humor4fun/NFC-Cartridge-Player/3d print files/mods/vhs_player_slot_w_support.stl

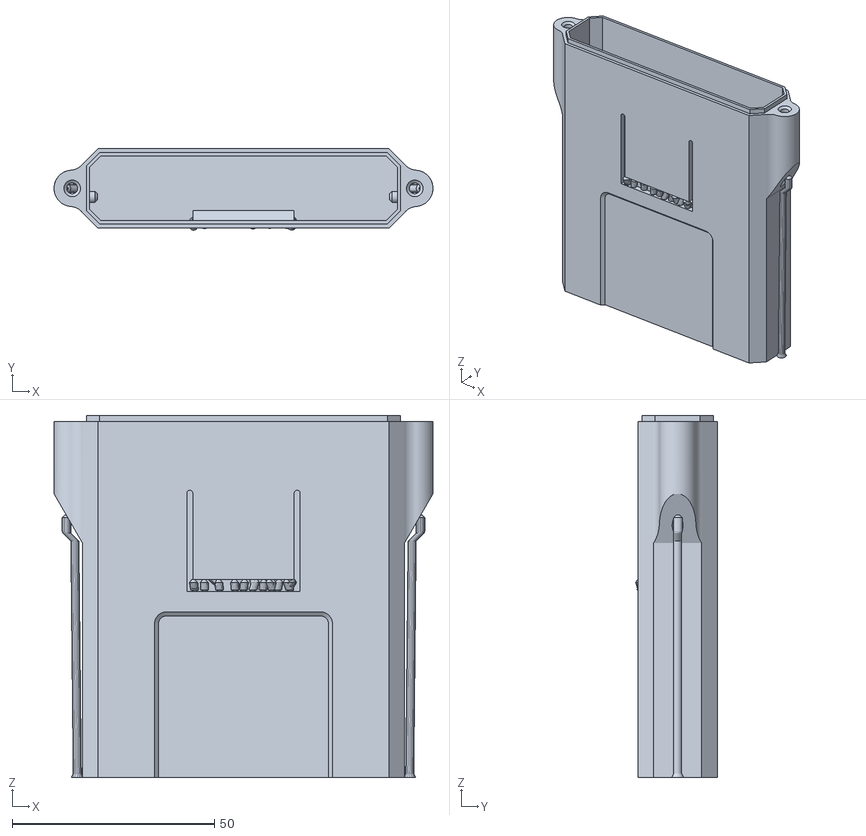
[picture p21: CAD file, 2026-01-05]
3d print files/mods/vhs_player_slot_w_support.stl
93.6 x 20.2 x 89.5
