humor4fun/NFC-Cartridge-Player/3d print files/Player/cartridge-player_bottom.3mf

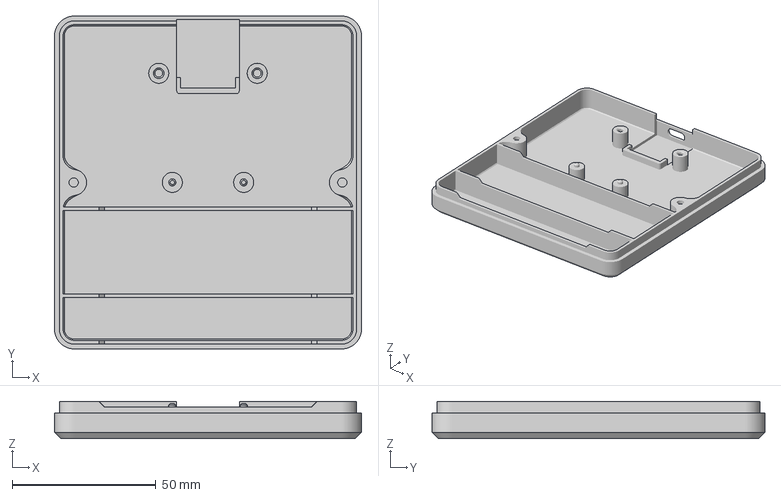
[picture p22: CAD file, 2026-01-05]
3d print files/Player/cartridge-player_bottom.3mf
107.0 x 116.0 x 13.0 mm
