humor4fun/NFC-Cartridge-Player/3d print files/Flip cartridge box/Cartridge/Cartridge+Top.stl

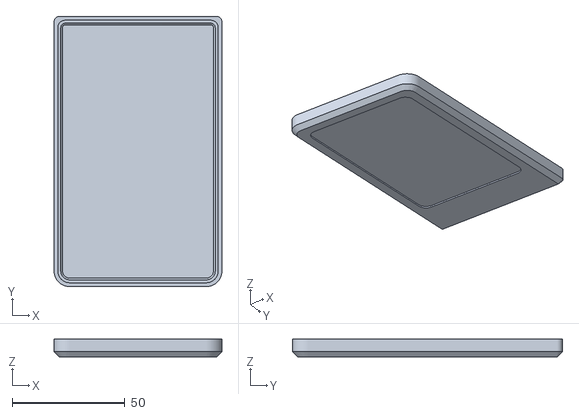
[picture p24: CAD file, 2026-01-05]
3d print files/Flip cartridge box/Cartridge/Cartridge+Top.stl
74.6 x 120.0 x 7.80
