humor4fun/NFC-Cartridge-Player/3d print files/mods/multi-part-cartridge/cartridge-label.stl

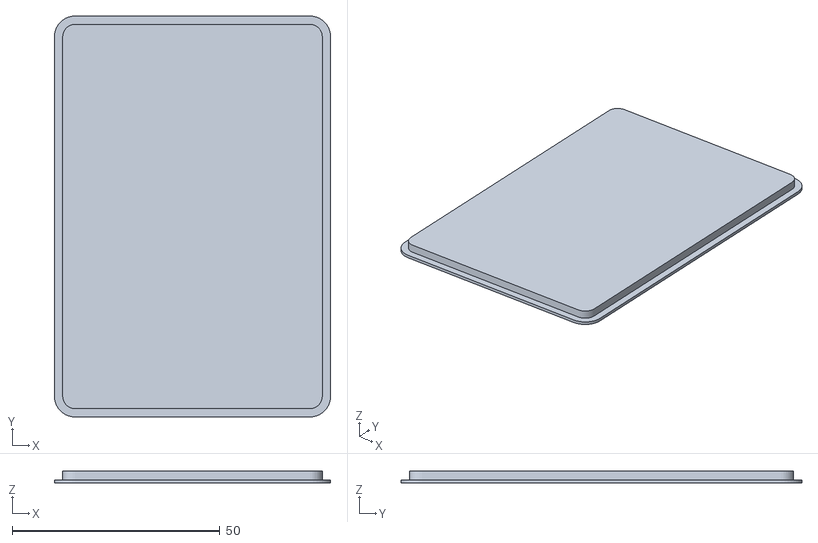
[picture p25: CAD file, 2026-01-05]
3d print files/mods/multi-part-cartridge/cartridge-label.stl
66.5 x 96.5 x 3.00
