humor4fun/NFC-Cartridge-Player/3d print files/Player/cartridge-player_bottom_buzzer.3mf

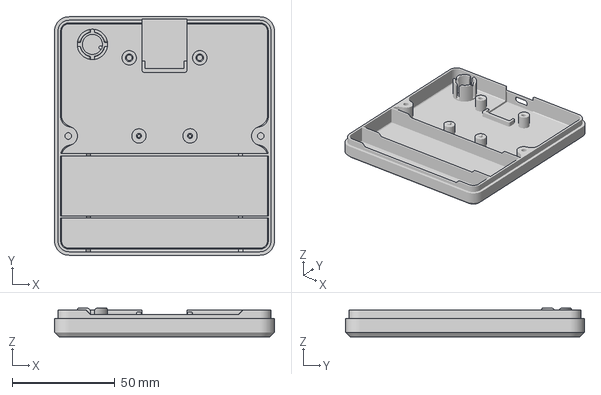
[picture p26: CAD file, 2026-01-05]
3d print files/Player/cartridge-player_bottom_buzzer.3mf
107.0 x 116.0 x 14.0 mm
