humor4fun/NFC-Cartridge-Player/3d print files/Flip cartridge box/Box/cartridge-box-8-slot.stl

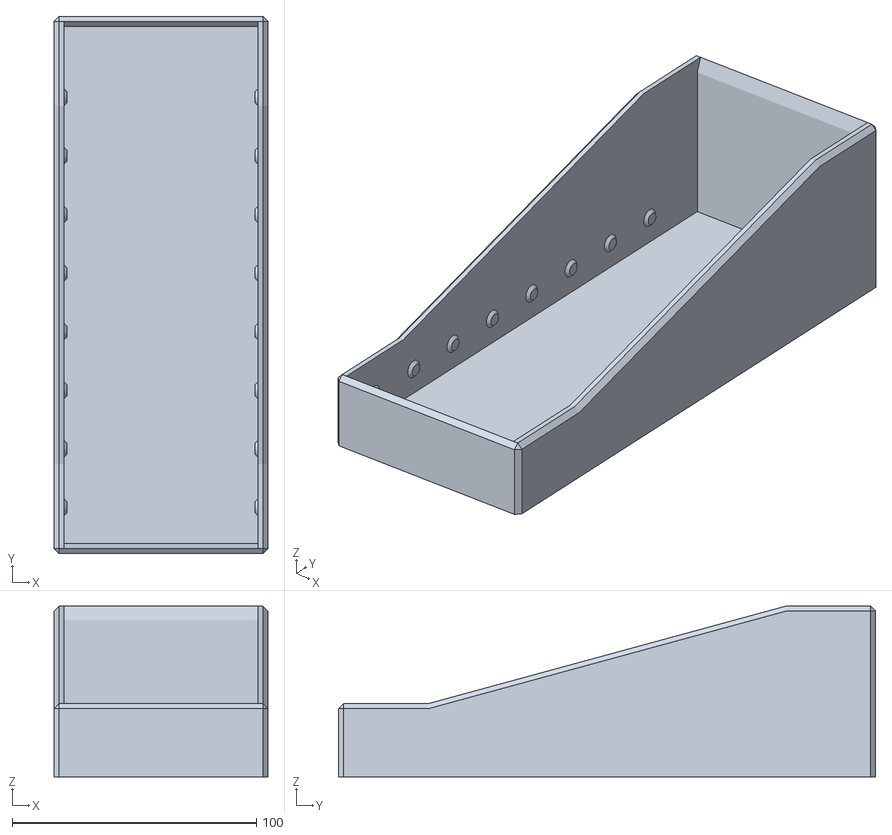
[picture p28: CAD file, 2026-01-05]
3d print files/Flip cartridge box/Box/cartridge-box-8-slot.stl
87.6 x 220.0 x 70.0
