humor4fun/NFC-Cartridge-Player/3d print files/Flip cartridge box/Box/stock-pot-cartridge-player-6-slots.3mf

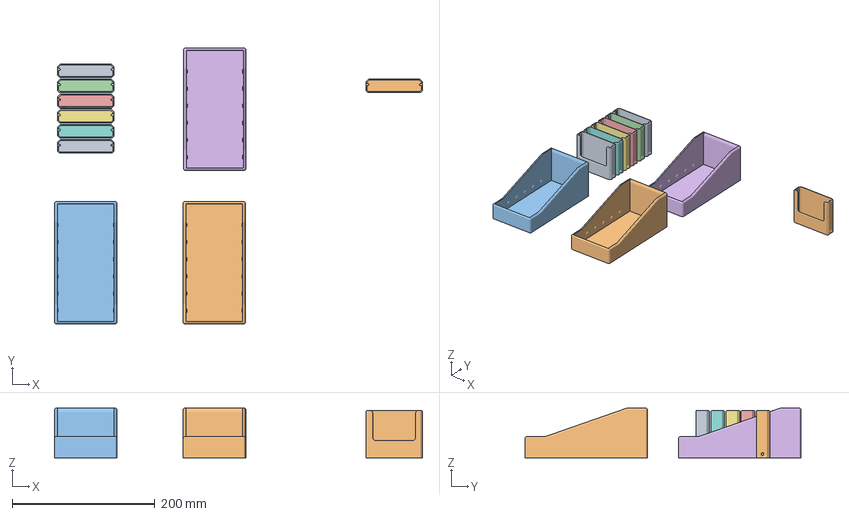
[picture p29: CAD file, 2026-01-05]
3d print files/Flip cartridge box/Box/stock-pot-cartridge-player-6-slots.3mf
515.4 x 387.0 x 70.0 mm
cartridge-slot.stl x 7
cartridge-box.stl x 3
