humor4fun/NFC-Cartridge-Player/3d print files/Flip cartridge box/Box/cartridge-box-6-slot.stl

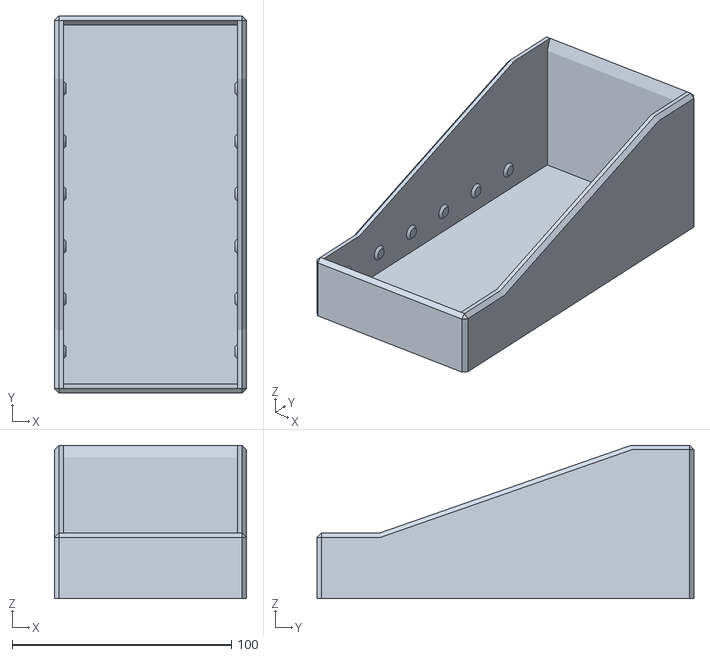
[picture p30: CAD file, 2026-01-05]
3d print files/Flip cartridge box/Box/cartridge-box-6-slot.stl
87.6 x 172.0 x 70.0
