humor4fun/NFC-Cartridge-Player/3d print files/Flip cartridge box/Box/cartridge-slot.stl

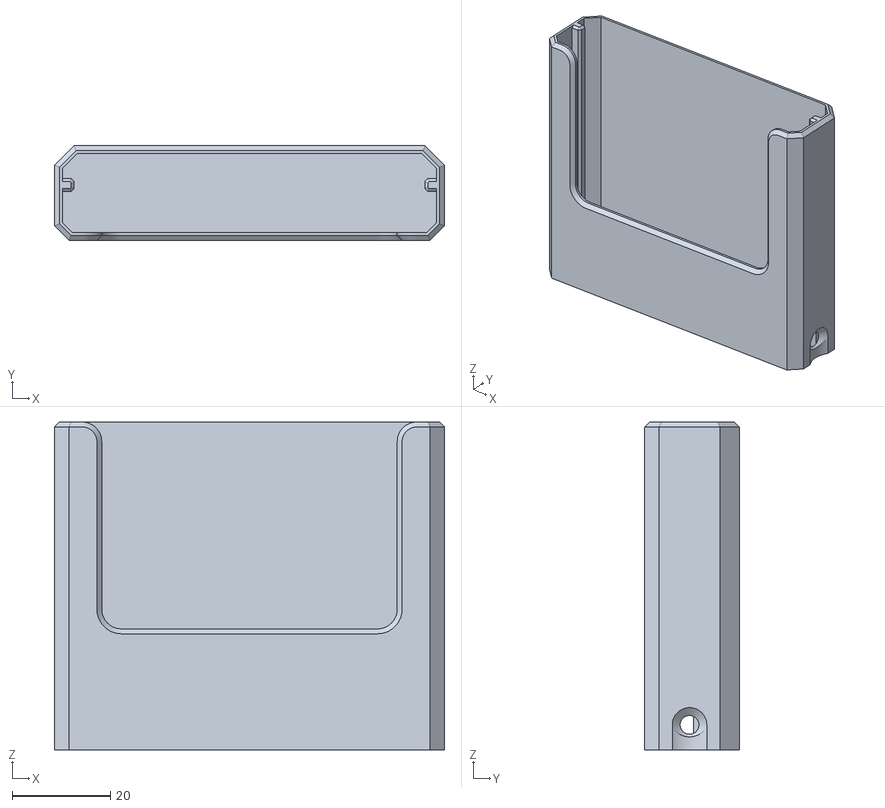
[picture p31: CAD file, 2026-01-05]
3d print files/Flip cartridge box/Box/cartridge-slot.stl
79.2 x 19.2 x 66.6
