humor4fun/NFC-Cartridge-Player/3d print files/Flip cartridge box/Box/cartridge-box-3-slot.stl

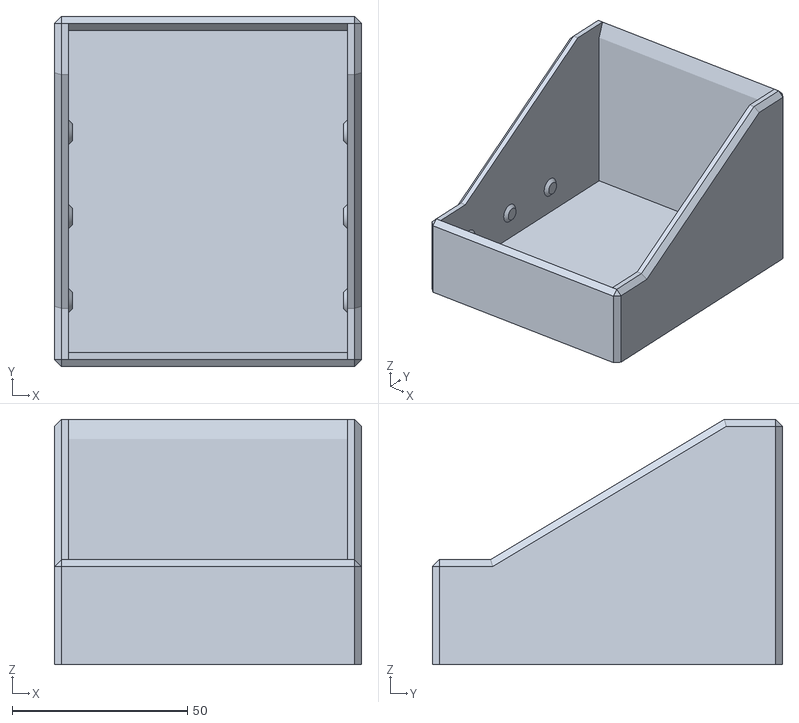
[picture p32: CAD file, 2026-01-05]
3d print files/Flip cartridge box/Box/cartridge-box-3-slot.stl
87.6 x 100.0 x 70.0
