humor4fun/NFC-Cartridge-Player/Wiring Diagrams/Wiring - ESP32-C3.jpg

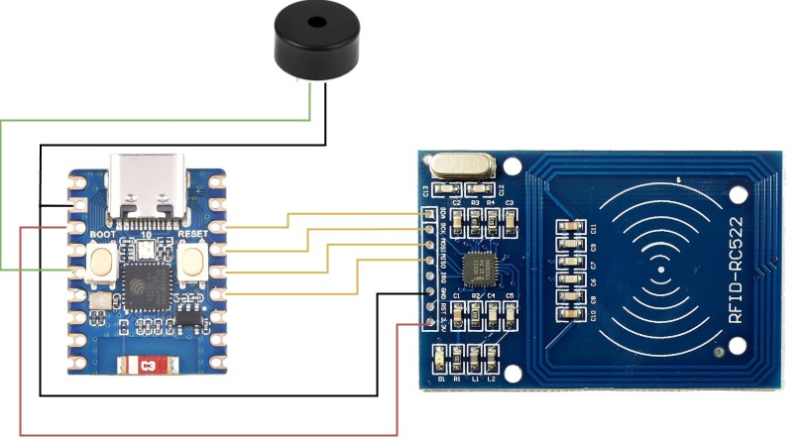
Wiring Diagrams/Wiring - ESP32-C3.jpg
